m5kro/KiKard/hardware/extra-symbols-footprints/3dshapes/SOT-723-3P_L1.2-W0.8-H0.6-LS1.2-P0.40.step

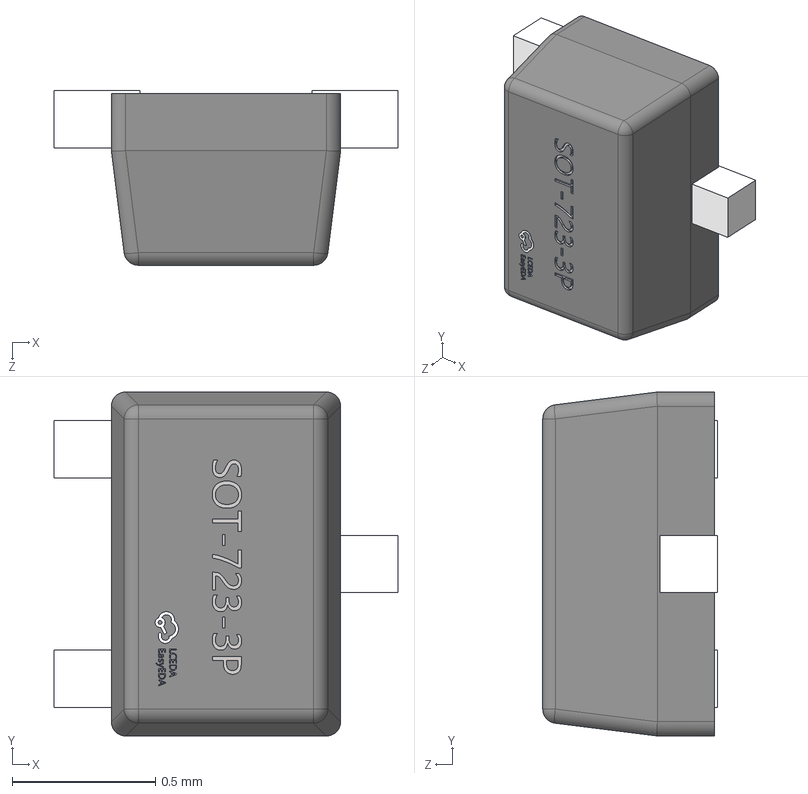
[picture p18: CAD file, 2025-07-11]
hardware/extra-symbols-footprints/3dshapes/SOT-723-3P_L1.2-W0.8-H0.6-LS1.2-P0.40.step
1.20 x 1.20 x 0.611 mm
