m5kro/KiKard/hardware/extra-symbols-footprints/3dshapes/ST25R3916-AQWT.step

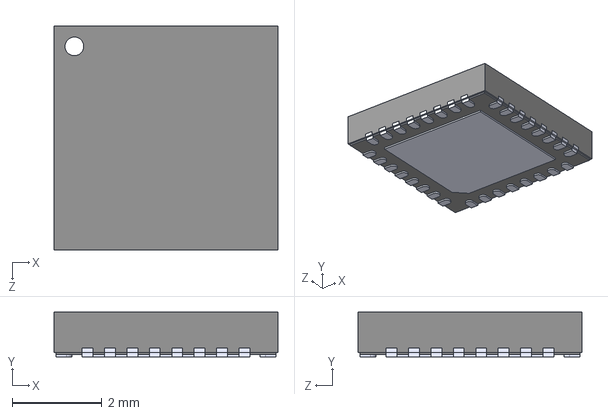
[picture p19: CAD file, 2025-06-03]
hardware/extra-symbols-footprints/3dshapes/ST25R3916-AQWT.step
5.00 x 1.00 x 5.00 mm
