m5kro/KiKard/hardware/extra-symbols-footprints/3dshapes/NRF52840-QIAA-R.step

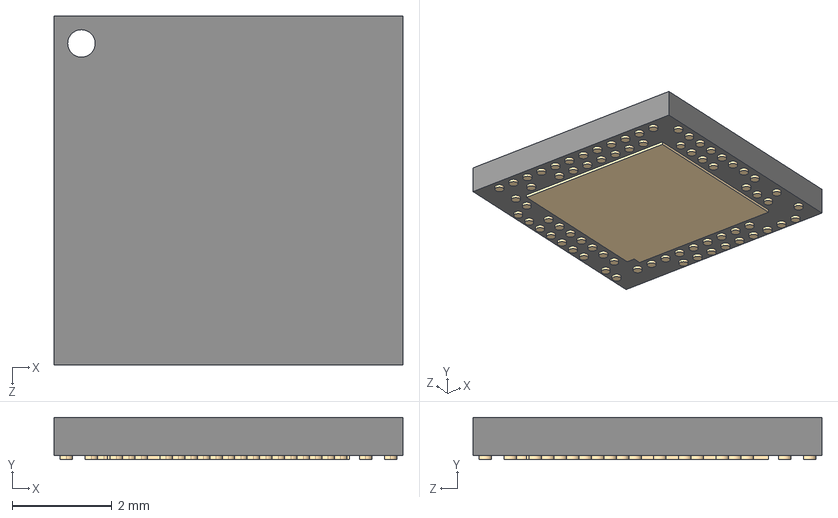
[picture p20: CAD file, 2025-06-01]
hardware/extra-symbols-footprints/3dshapes/NRF52840-QIAA-R.step
7.00 x 0.85 x 7.00 mm
